JiriKupka/gramik/assets/disc-images/animals1.png

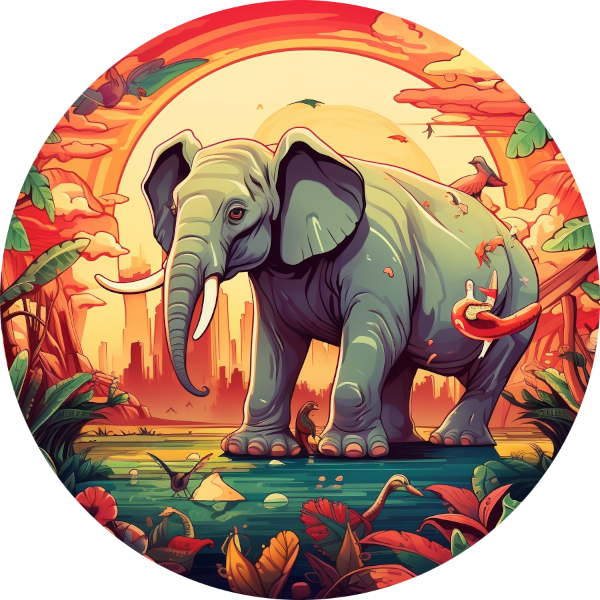
assets/disc-images/animals1.png
