JiriKupka/gramik/assets/disc-images/blank1.png

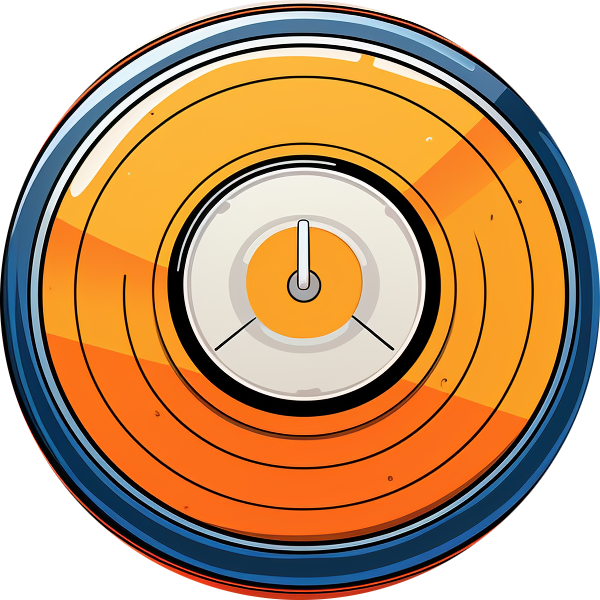
assets/disc-images/blank1.png
