JiriKupka/gramik/assets/disc-images/blank2.png

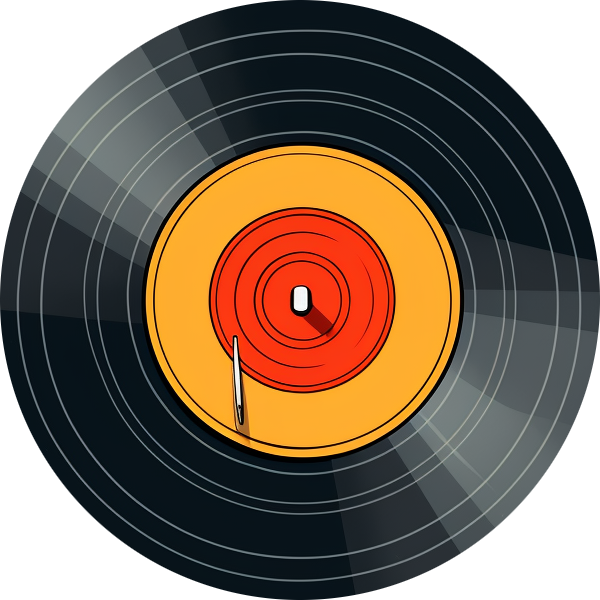
assets/disc-images/blank2.png
