JiriKupka/gramik/assets/disc-images/blank3.png

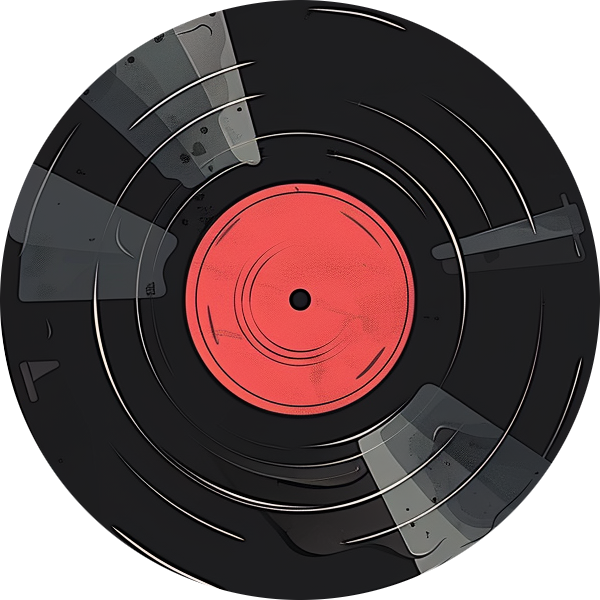
assets/disc-images/blank3.png
