JiriKupka/gramik/assets/disc-images/blank4.png

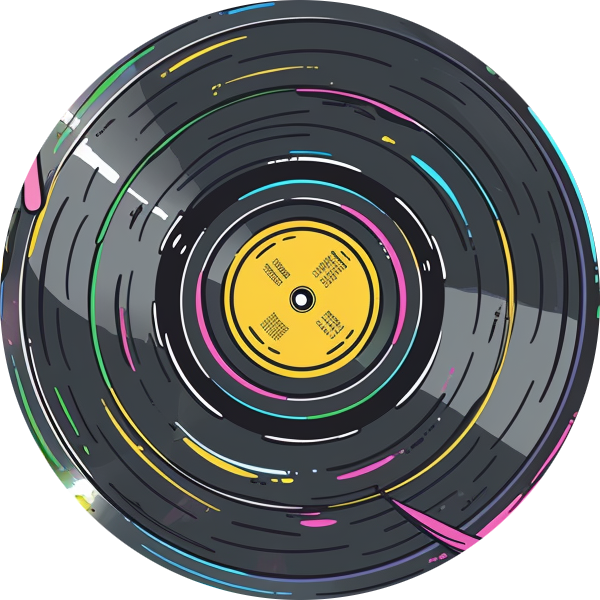
assets/disc-images/blank4.png
