JiriKupka/gramik/assets/disc-images/blank5.png

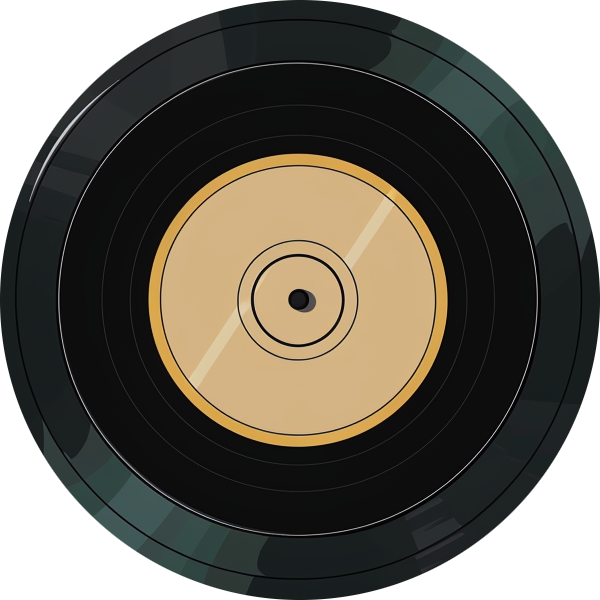
assets/disc-images/blank5.png
