JiriKupka/gramik/assets/disc-images/cars.png

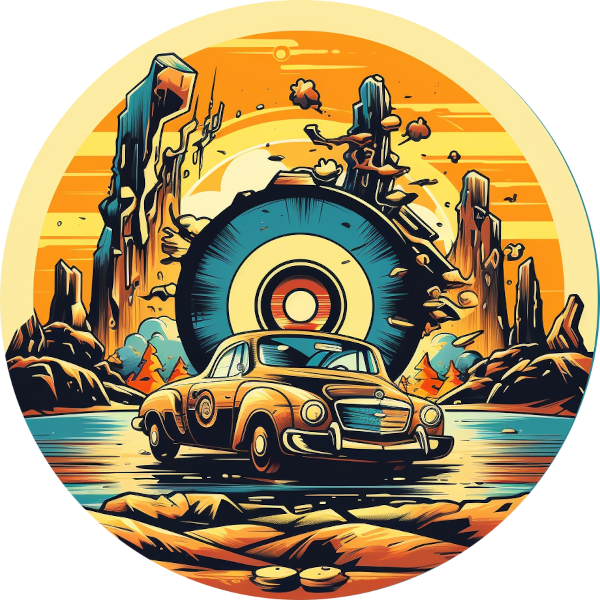
assets/disc-images/cars.png
