JiriKupka/gramik/assets/disc-images/classical1.png

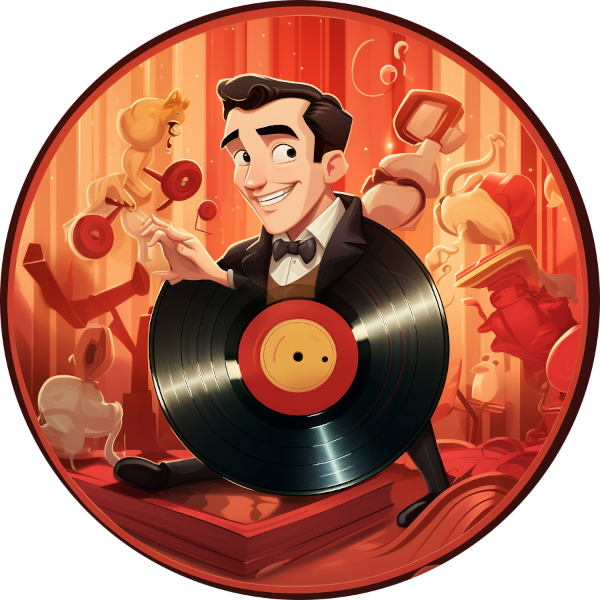
assets/disc-images/classical1.png
