JiriKupka/gramik/assets/disc-images/kids1.png

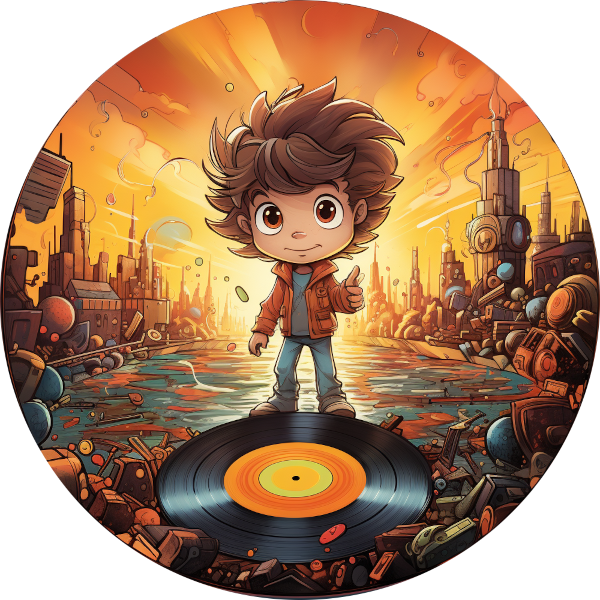
assets/disc-images/kids1.png
