JiriKupka/gramik/assets/disc-images/kids3.png

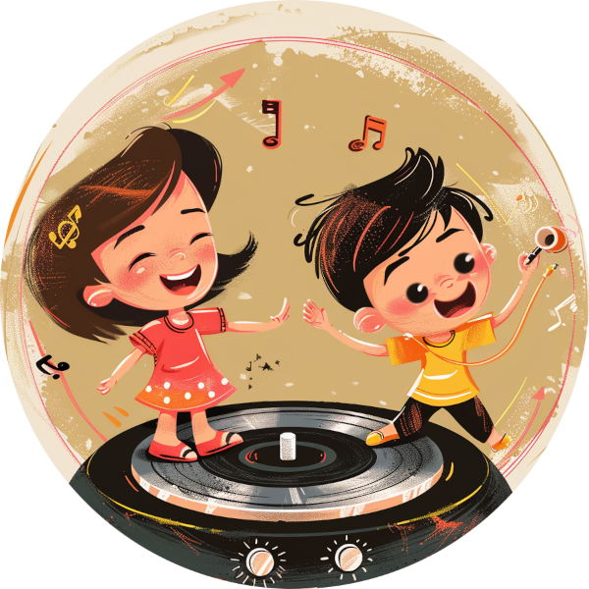
assets/disc-images/kids3.png
