JiriKupka/gramik/assets/disc-images/kids5.png

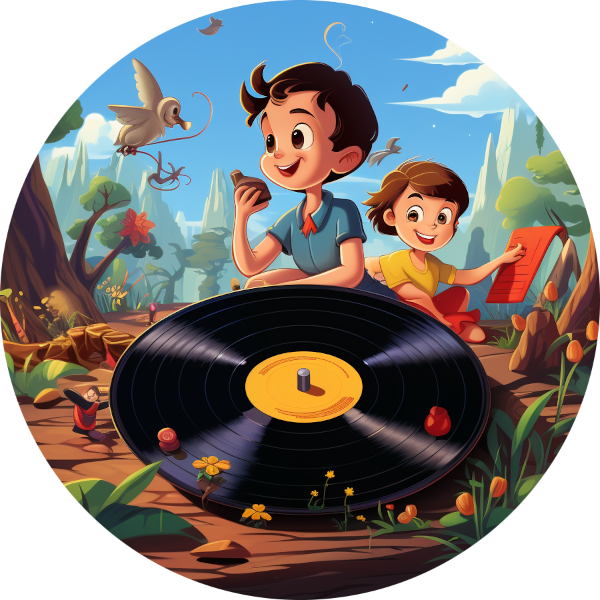
assets/disc-images/kids5.png
