JiriKupka/gramik/assets/disc-images/kids6.png

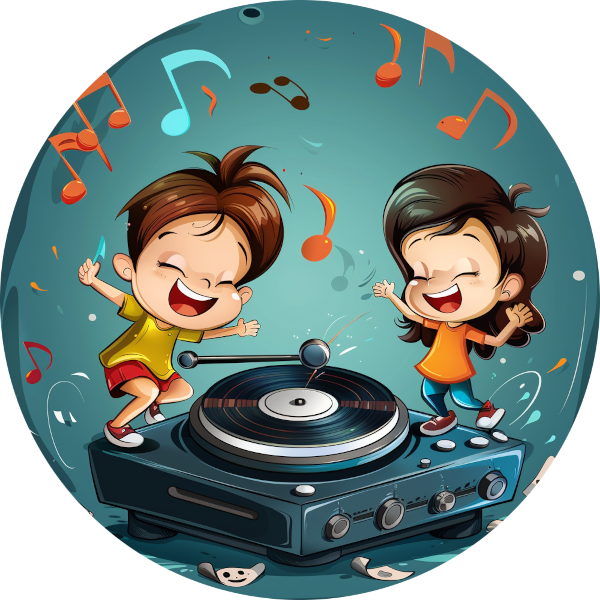
assets/disc-images/kids6.png
