JiriKupka/gramik/assets/disc-images/rocknroll-baby.png

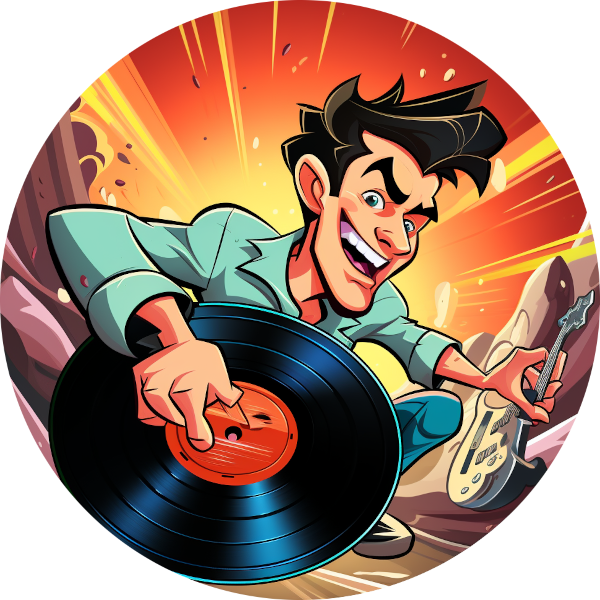
assets/disc-images/rocknroll-baby.png
