JiriKupka/gramik/assets/mc-images/amadeus.png

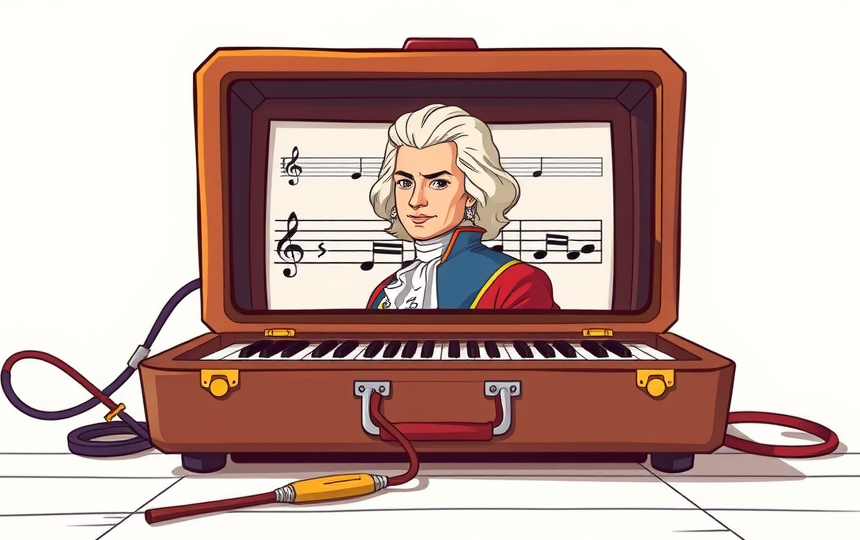
assets/mc-images/amadeus.png
