JiriKupka/gramik/assets/mc-images/animals.png

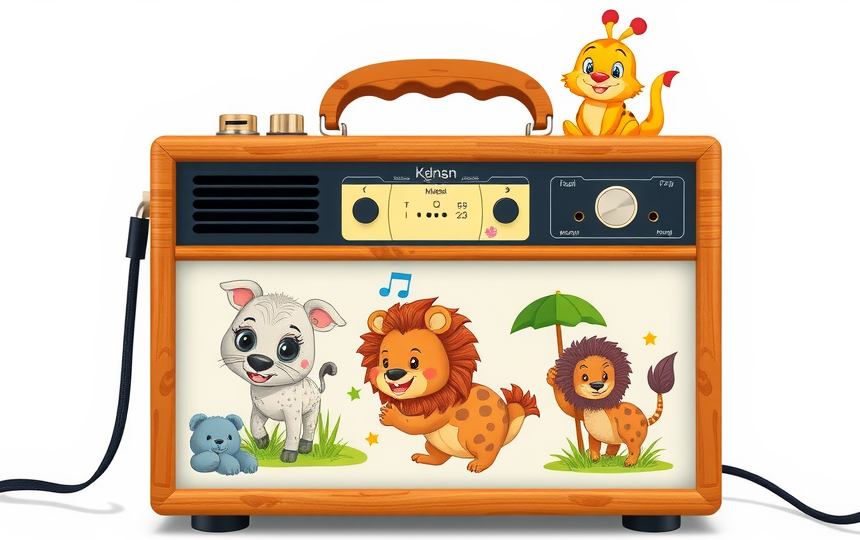
assets/mc-images/animals.png
