JiriKupka/gramik/assets/mc-images/bears.png

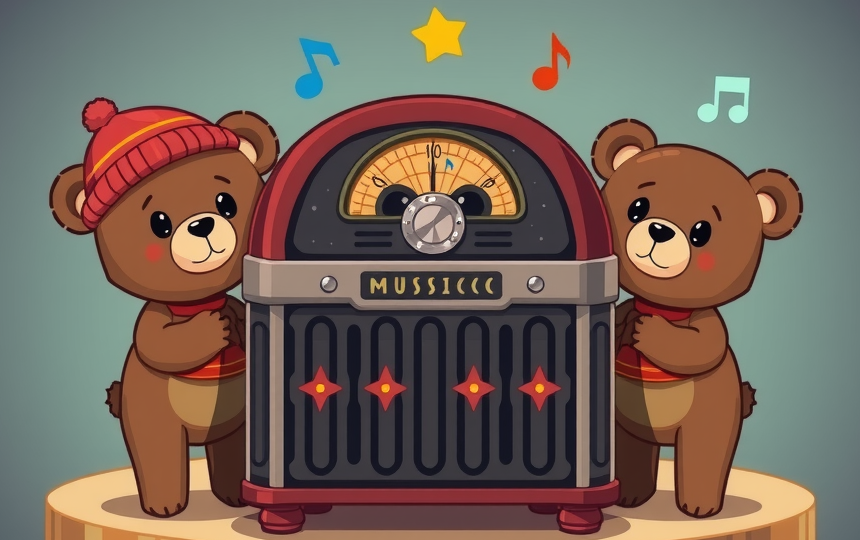
assets/mc-images/bears.png
