JiriKupka/gramik/assets/mc-images/classical.png

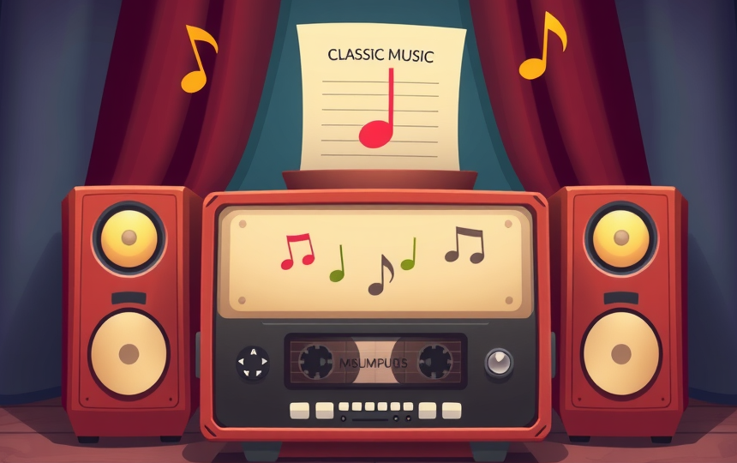
assets/mc-images/classical.png
