JiriKupka/gramik/assets/mc-images/dogs2.png

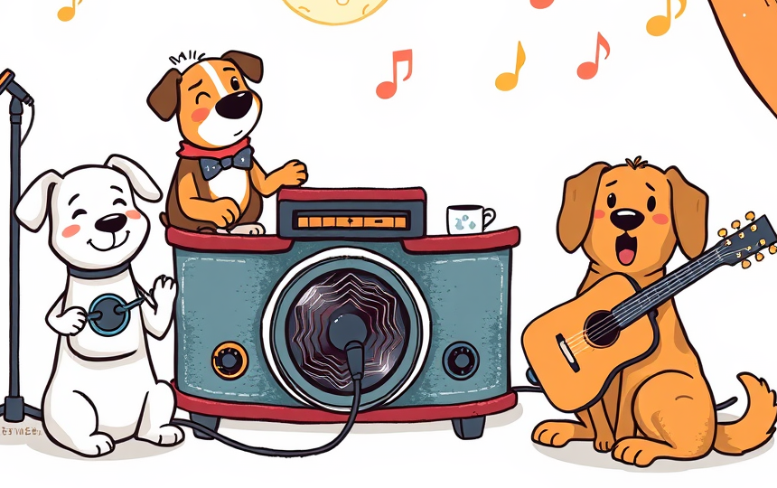
assets/mc-images/dogs2.png
