JiriKupka/gramik/assets/mc-images/fish2.png

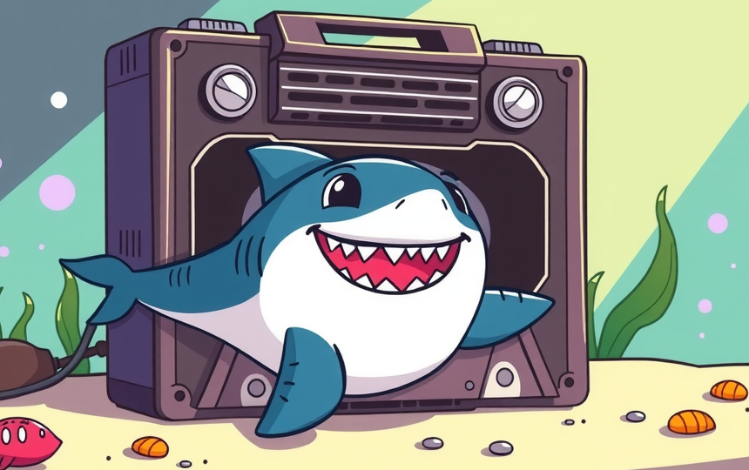
assets/mc-images/fish2.png
