JiriKupka/gramik/assets/mc-images/fish.png

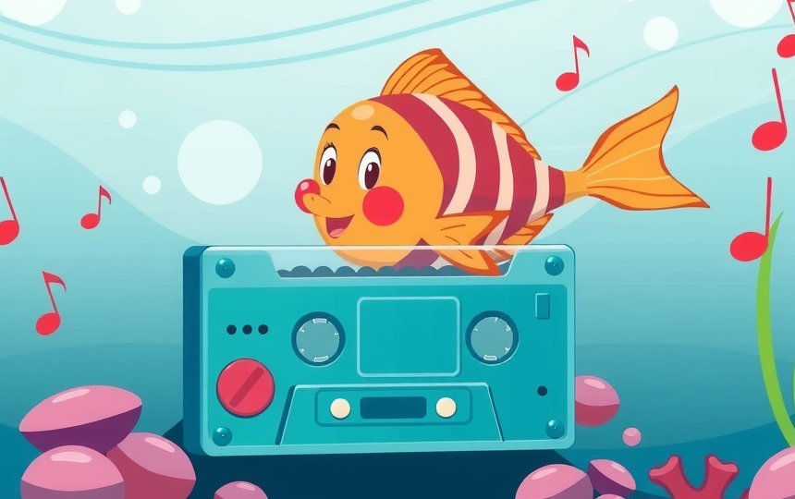
assets/mc-images/fish.png
