JiriKupka/gramik/assets/mc-images/guitar-boy.png

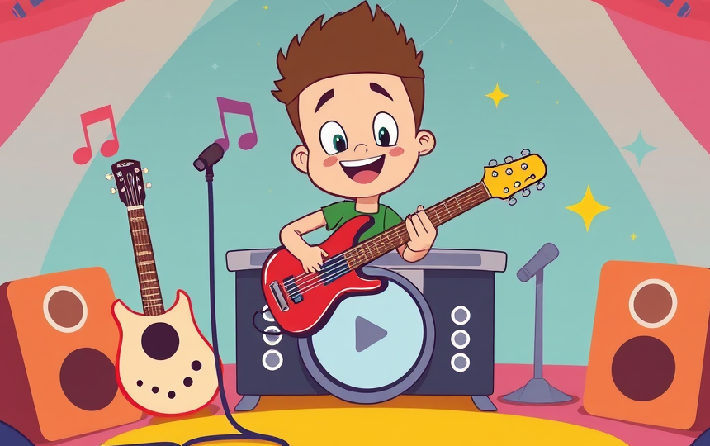
assets/mc-images/guitar-boy.png
