JiriKupka/gramik/assets/mc-images/horror.png

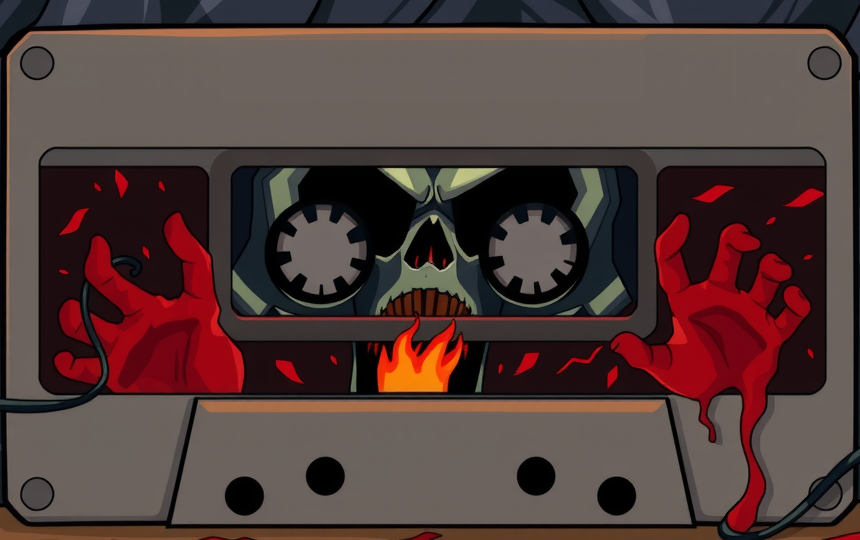
assets/mc-images/horror.png
