JiriKupka/gramik/assets/mc-images/paw.png

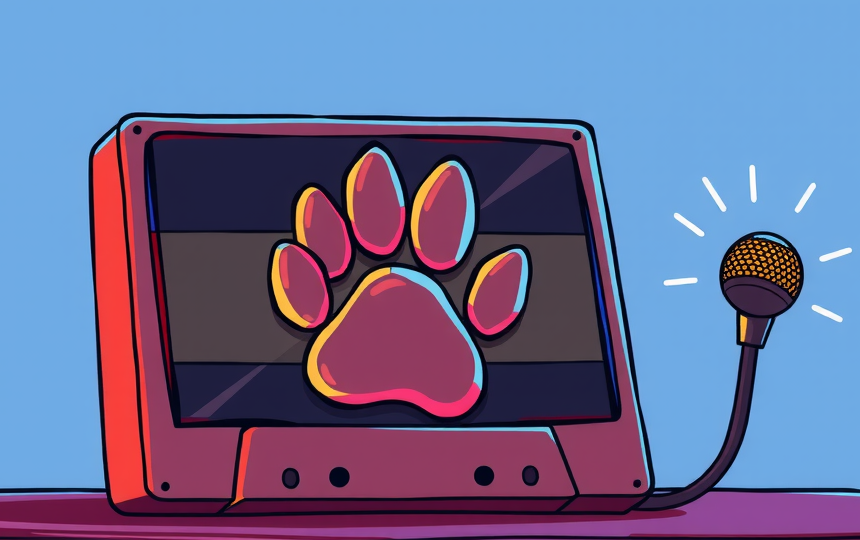
assets/mc-images/paw.png
