JiriKupka/gramik/assets/mc-images/police.png

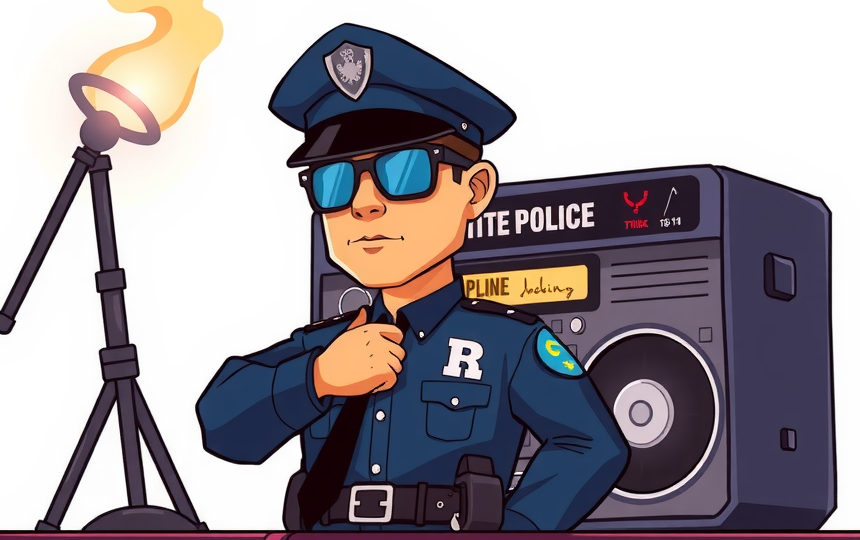
assets/mc-images/police.png
