JiriKupka/gramik/assets/mc-images/princesses2.png

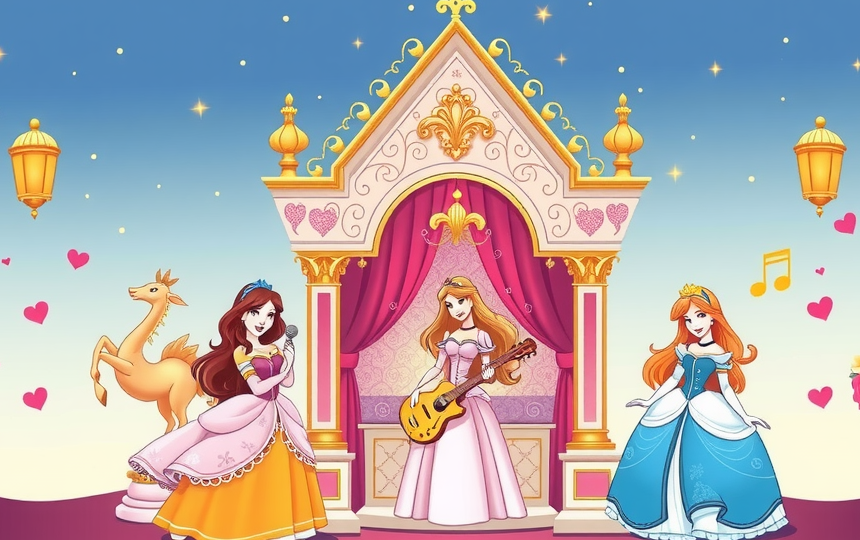
assets/mc-images/princesses2.png
