JiriKupka/gramik/assets/mc-images/princesses3.png

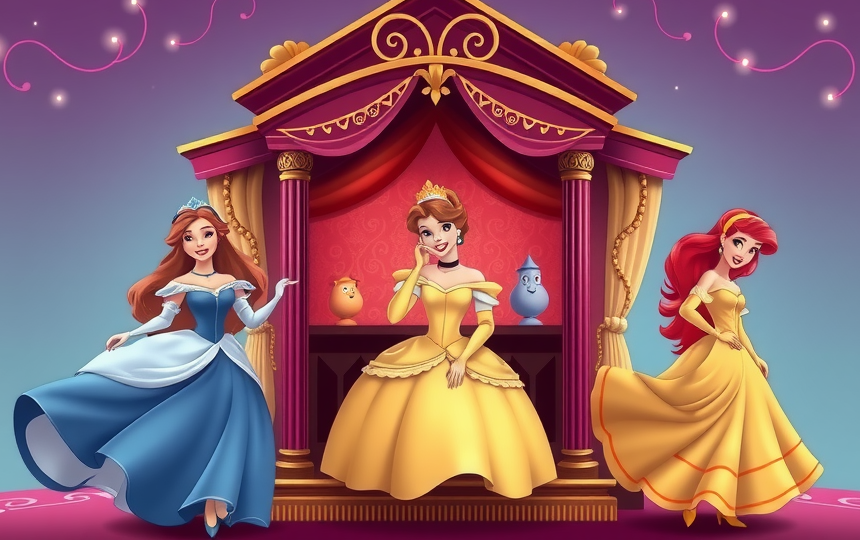
assets/mc-images/princesses3.png
