JiriKupka/gramik/assets/mc-images/princesses.png

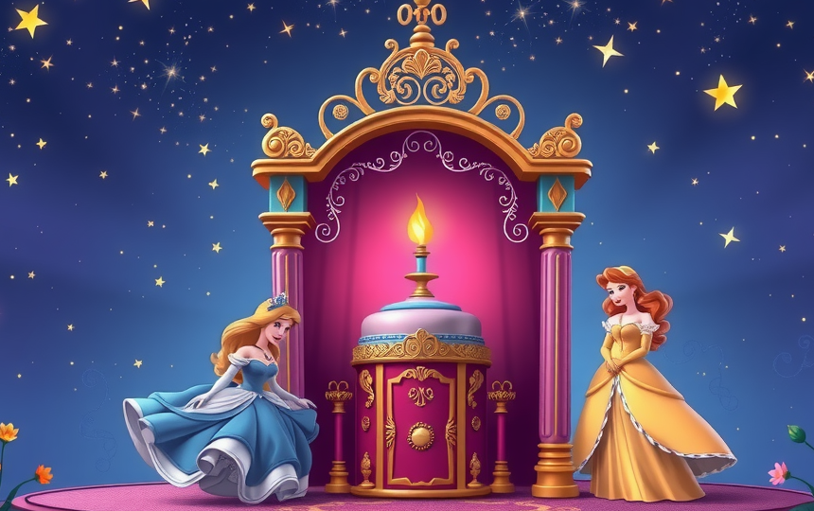
assets/mc-images/princesses.png
