JiriKupka/gramik/assets/mc-images/radio.png

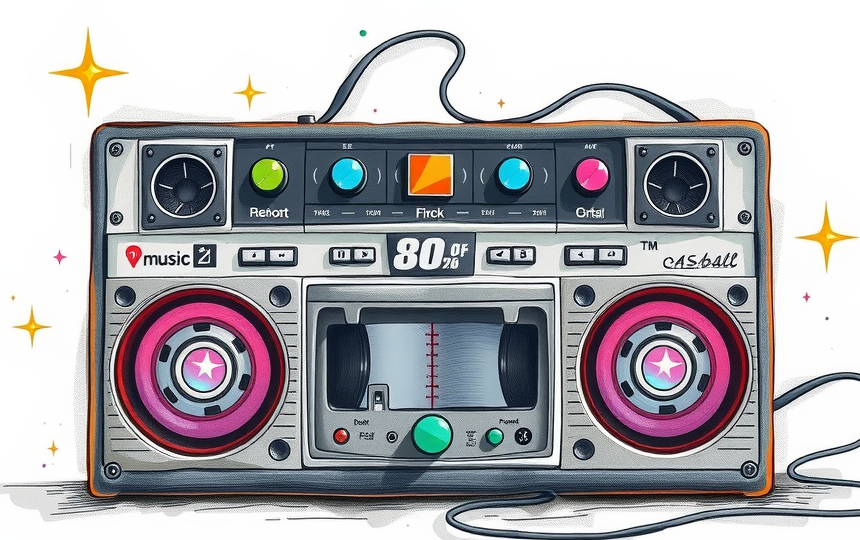
assets/mc-images/radio.png
