JiriKupka/gramik/assets/mc-images/rnr.png

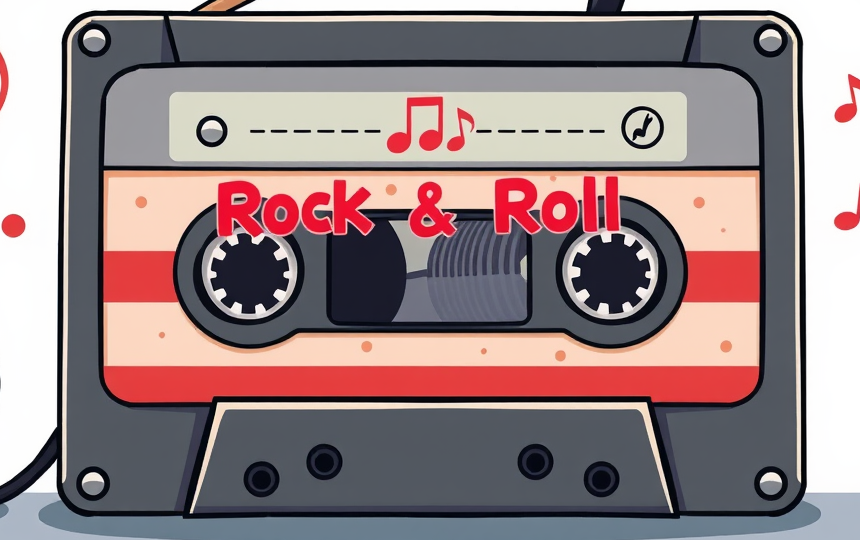
assets/mc-images/rnr.png
