JiriKupka/gramik/assets/mc-images/simple.png

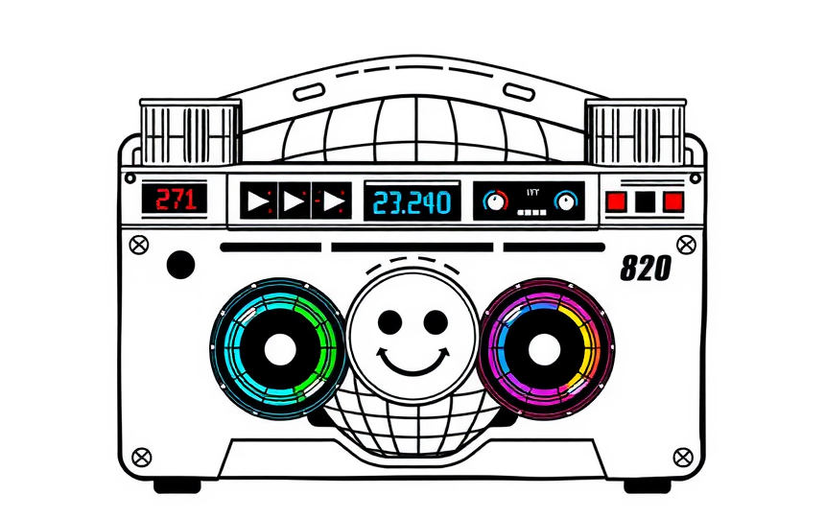
assets/mc-images/simple.png
