JiriKupka/gramik/assets/mc-images/smrf.png

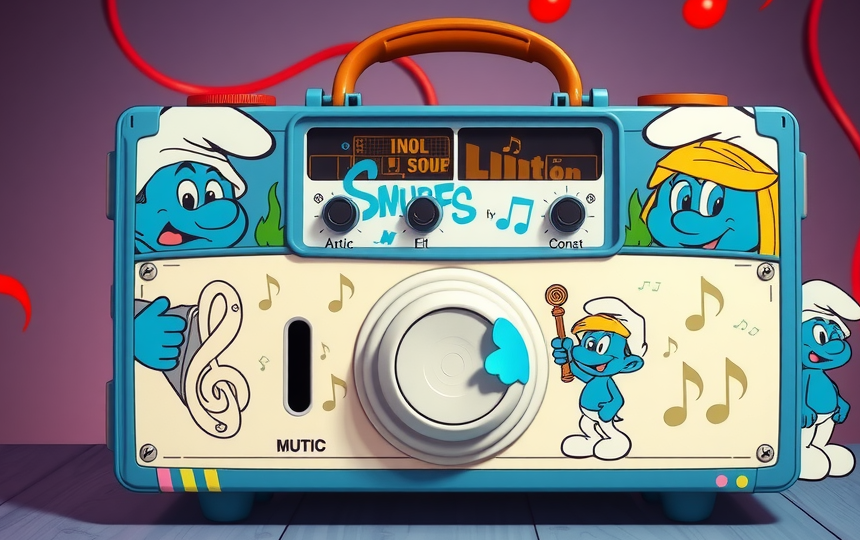
assets/mc-images/smrf.png
