JiriKupka/gramik/assets/mc-images/stereo2.png

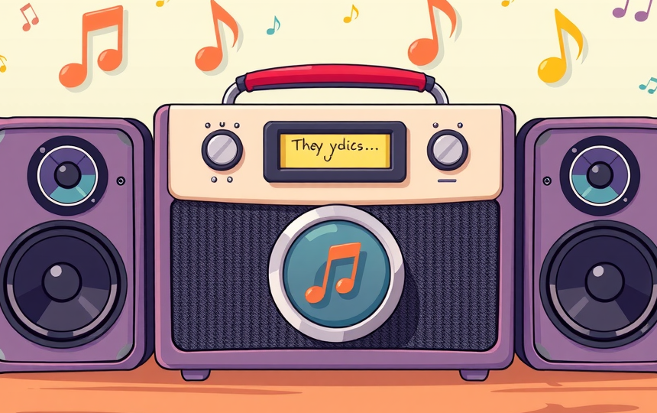
assets/mc-images/stereo2.png
