JiriKupka/gramik/assets/mc-images/stereo3.png

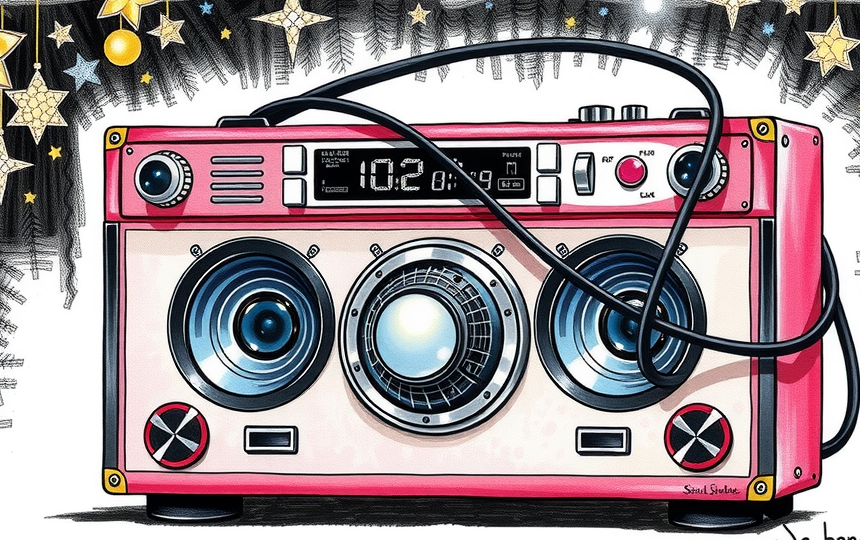
assets/mc-images/stereo3.png
