JiriKupka/gramik/assets/mc-images/stereo.png

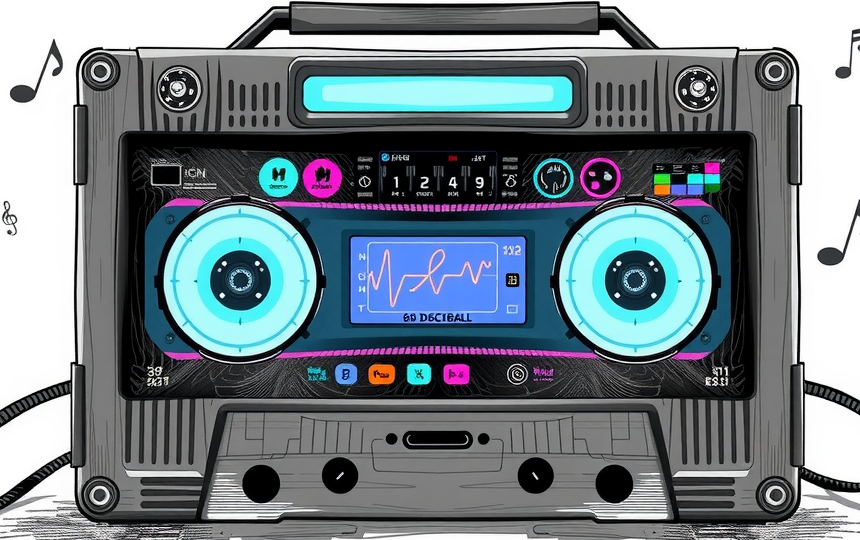
assets/mc-images/stereo.png
