JiriKupka/gramik/assets/mc-images/superheroes.png

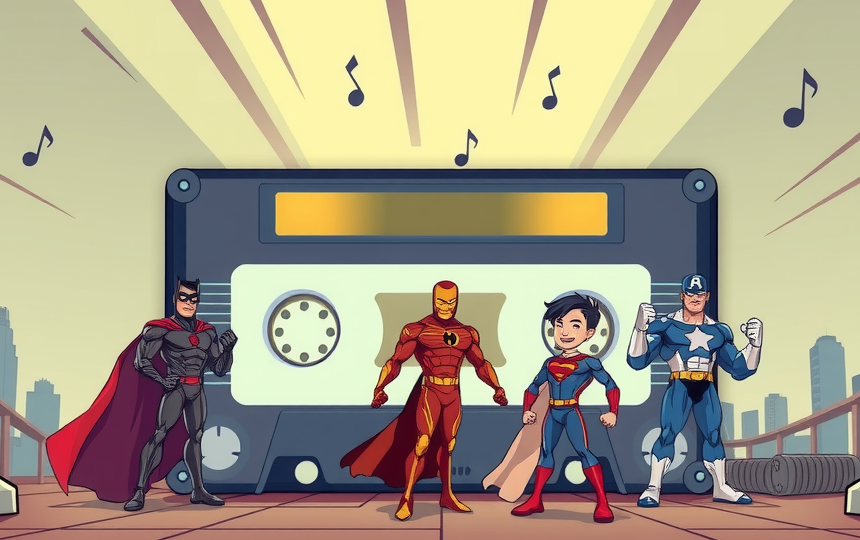
assets/mc-images/superheroes.png
