JiriKupka/gramik/imgs/gramik03_alpha.webp

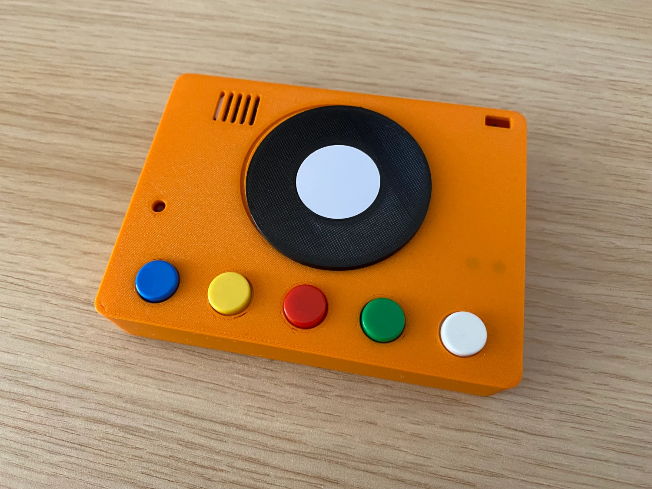
imgs/gramik03_alpha.webp
