JiriKupka/gramik/imgs/gramik_01.webp

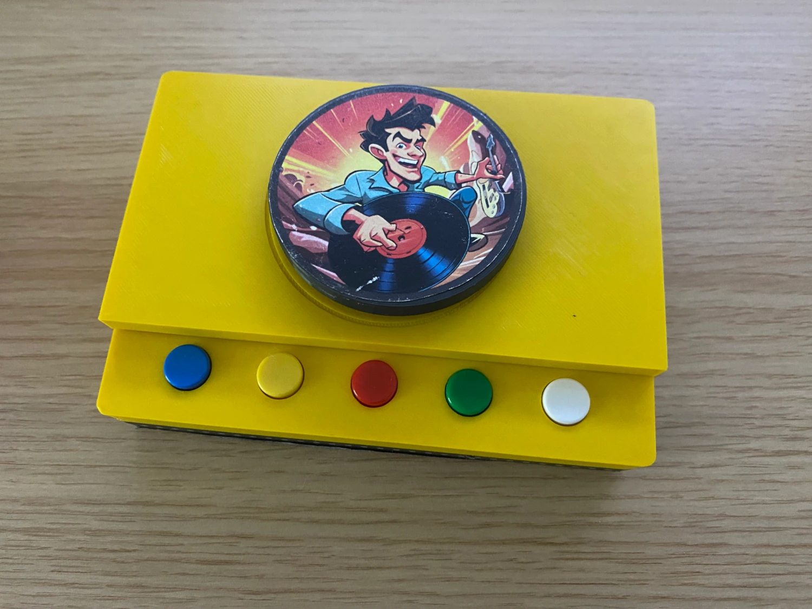
imgs/gramik_01.webp
