JiriKupka/gramik/imgs/gramik_03_pcb.webp

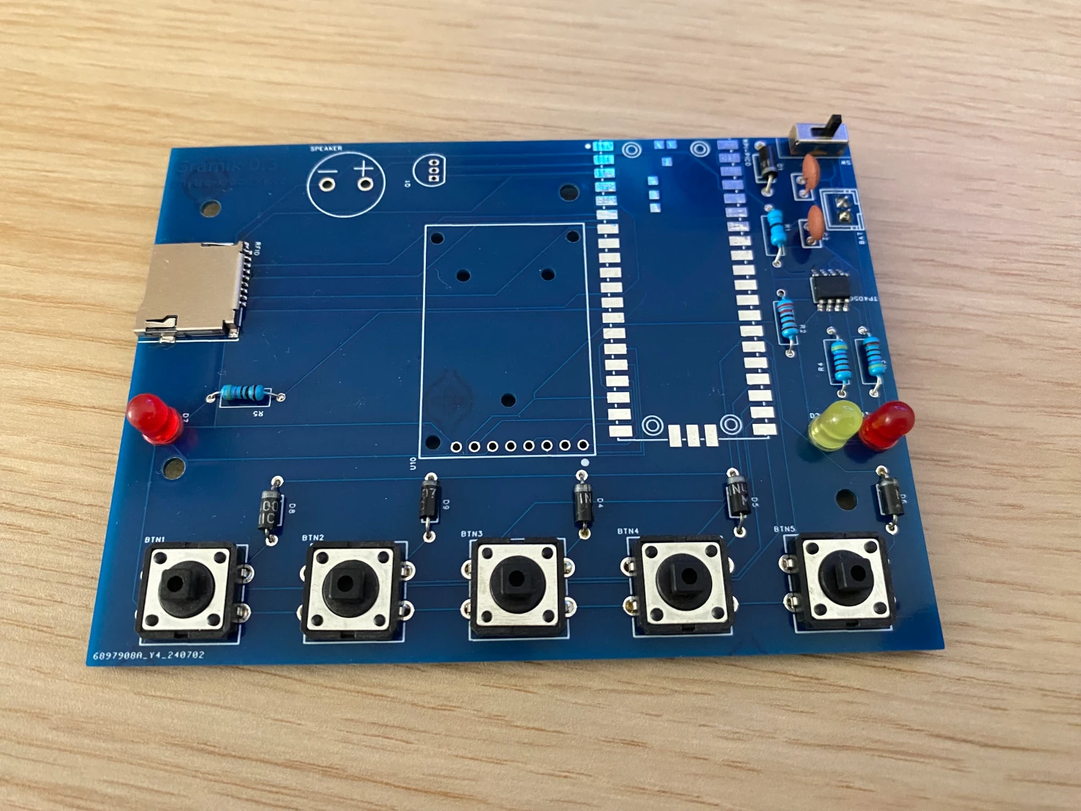
imgs/gramik_03_pcb.webp
