JiriKupka/gramik/imgs/gramik_vvelcro.webp

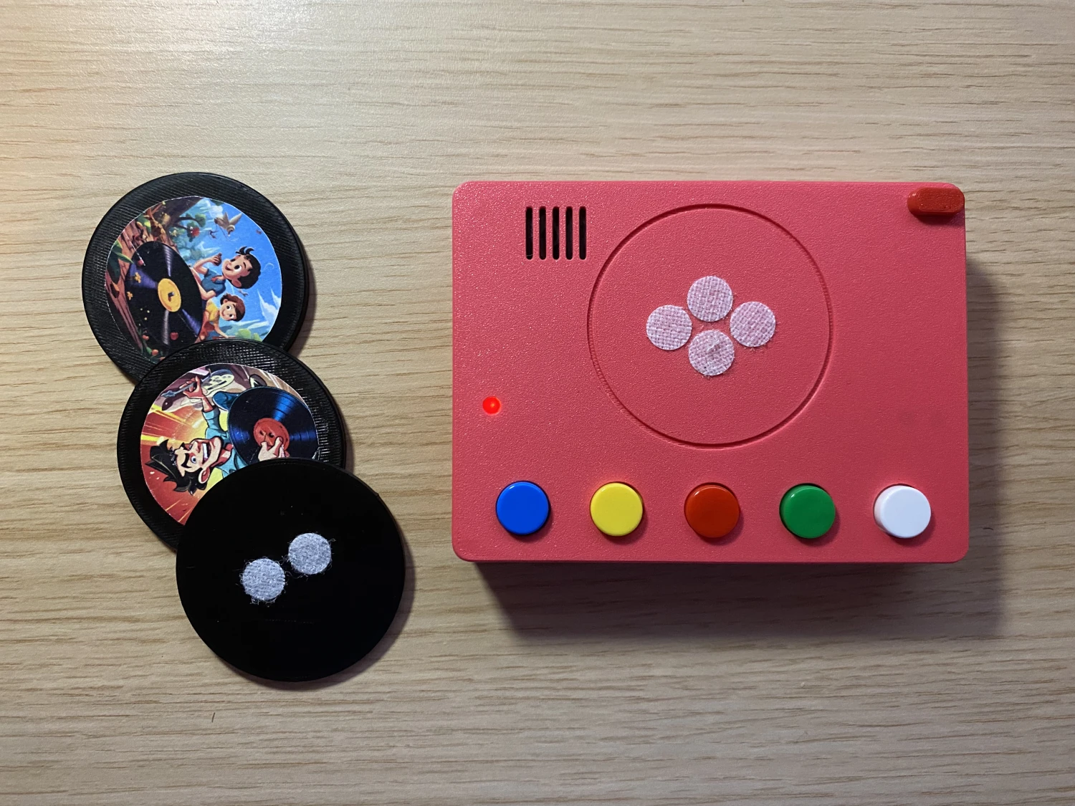
imgs/gramik_vvelcro.webp
